hukriede/Ocean-Technology-Club/docs/images/diagrams/granular/AboveSdDiagram.png

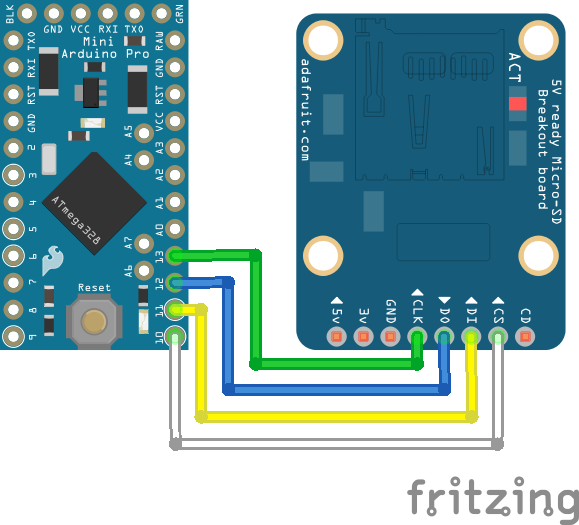
docs/images/diagrams/granular/AboveSdDiagram.png
