hukriede/Ocean-Technology-Club/docs/images/diagrams/granular/BelowDiagram.png

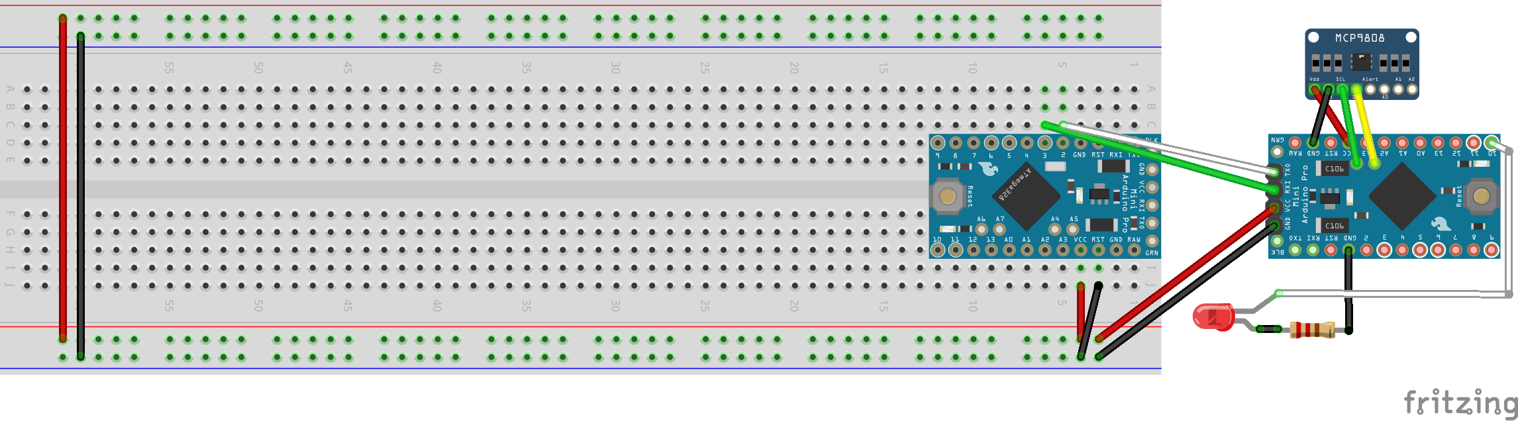
docs/images/diagrams/granular/BelowDiagram.png
