hukriede/Ocean-Technology-Club/docs/images/diagrams/granular/WifiDiagram.png

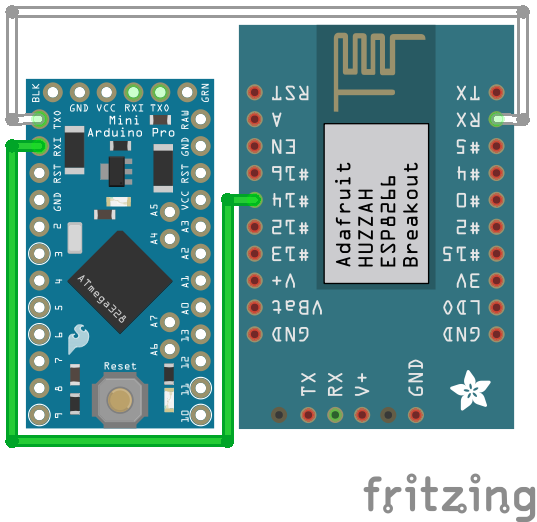
docs/images/diagrams/granular/WifiDiagram.png
