hukriede/Ocean-Technology-Club/docs/images/diagrams/SensorsDiagram.png

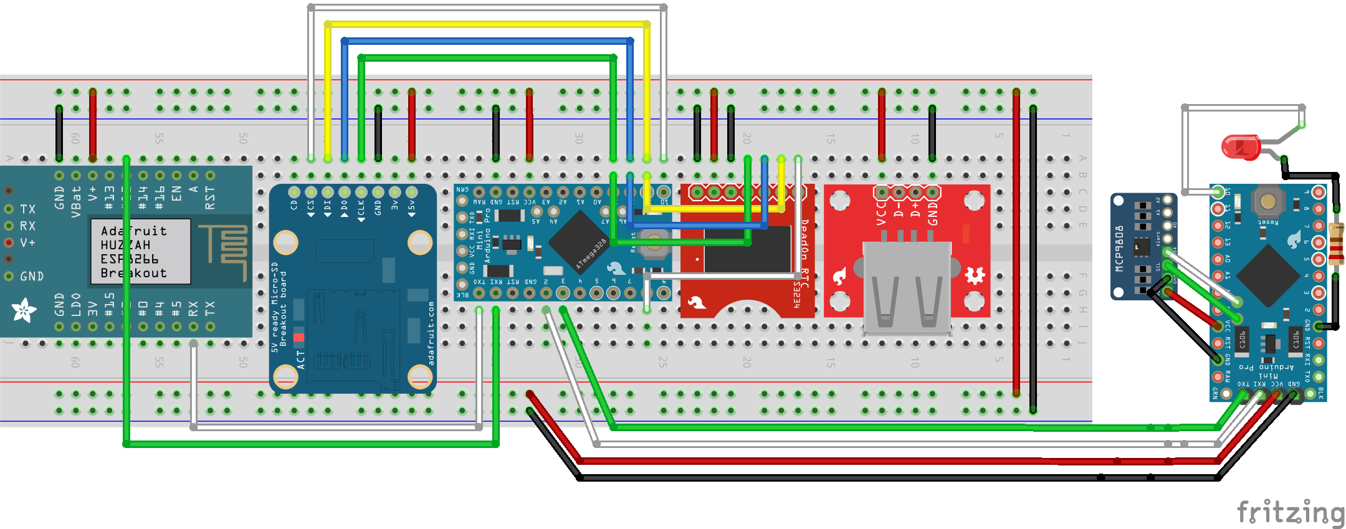
docs/images/diagrams/SensorsDiagram.png
