hukriede/Ocean-Technology-Club/docs/images/housing/crimp.jpg

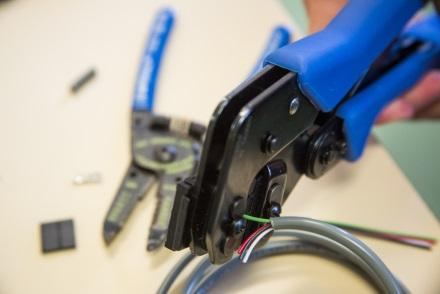
docs/images/housing/crimp.jpg
