hukriede/Ocean-Technology-Club/docs/images/housing/glue.jpg

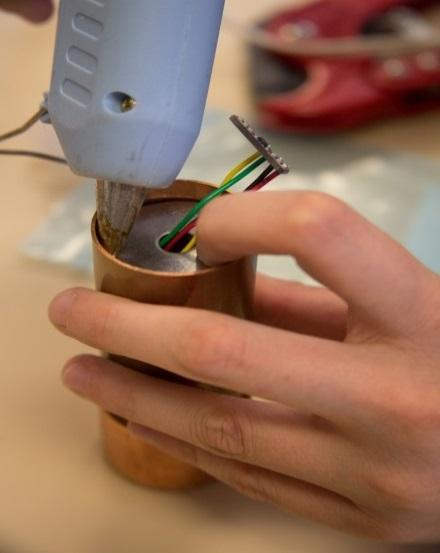
docs/images/housing/glue.jpg
