hukriede/Ocean-Technology-Club/docs/images/housing/heat.jpg

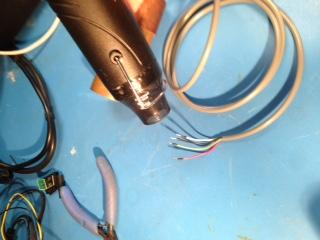
docs/images/housing/heat.jpg
