hukriede/Ocean-Technology-Club/docs/images/housing/strip.jpg

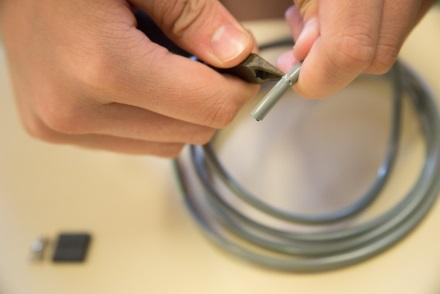
docs/images/housing/strip.jpg
