hukriede/Ocean-Technology-Club/docs/images/housing/parts.jpg

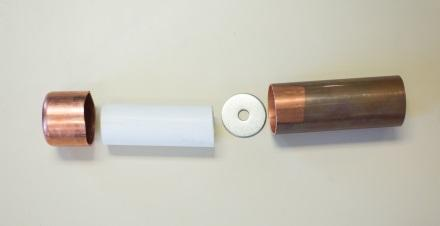
docs/images/housing/parts.jpg
