hukriede/Ocean-Technology-Club/docs/images/wiring/arduinoSolder.jpg

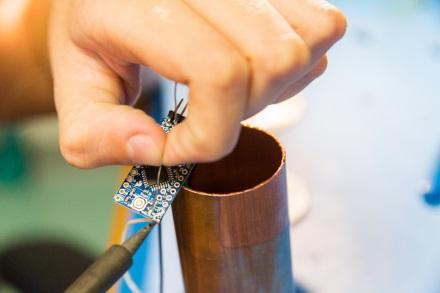
docs/images/wiring/arduinoSolder.jpg
