hukriede/Ocean-Technology-Club/docs/images/wiring/enclosure.jpg

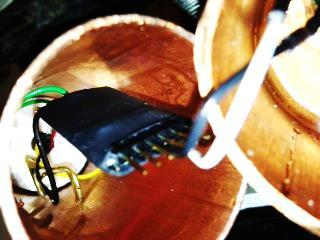
docs/images/wiring/enclosure.jpg
