hukriede/Ocean-Technology-Club/docs/images/wiring/housing.jpg

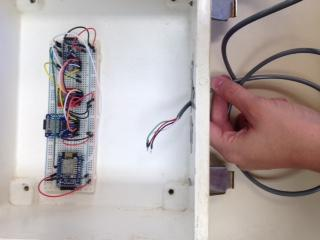
docs/images/wiring/housing.jpg
