hukriede/Ocean-Technology-Club/docs/images/wiring/ledSolder.jpg

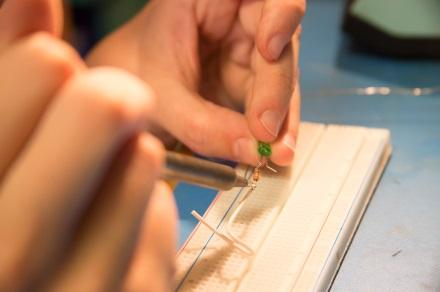
docs/images/wiring/ledSolder.jpg
