hukriede/Ocean-Technology-Club/docs/images/wiring/solder.jpg

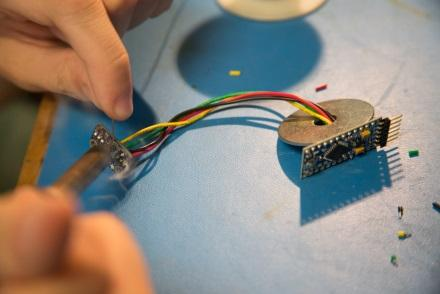
docs/images/wiring/solder.jpg
