hukriede/Ocean-Technology-Club/docs/images/wiring/tools.jpg

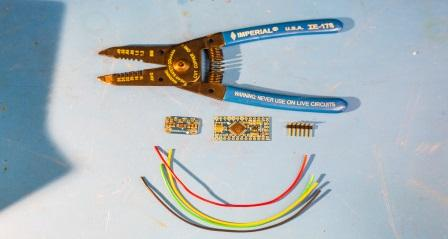
docs/images/wiring/tools.jpg
