hukriede/Ocean-Technology-Club/docs/images/wiring/washer.jpg

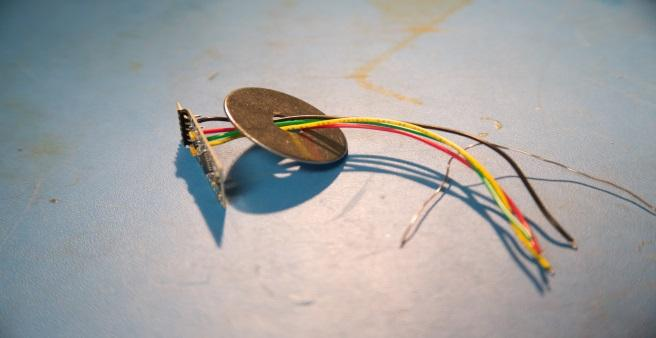
docs/images/wiring/washer.jpg
